jerryok826/rover-monitor/images/jpl_rover_1.jpeg

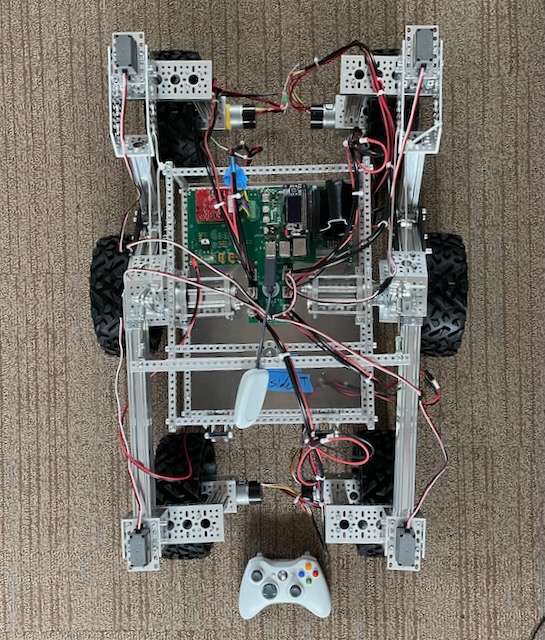
images/jpl_rover_1.jpeg
