jerryok826/rover-monitor/images/oled_board_back.jpeg

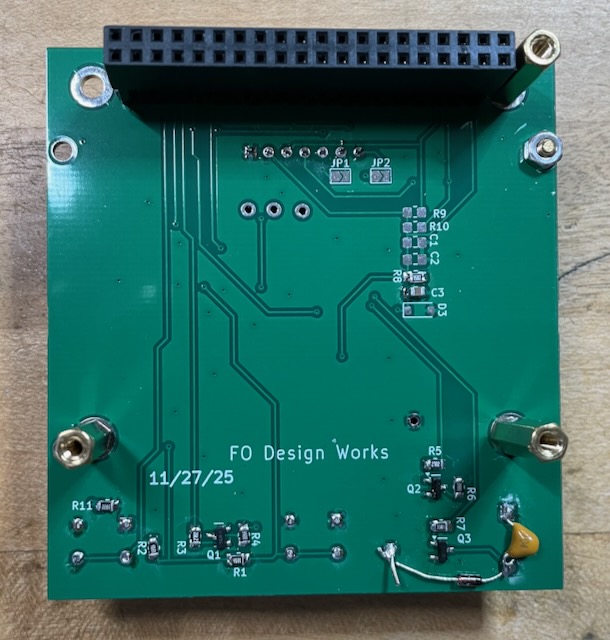
images/oled_board_back.jpeg
