jerryok826/rover-monitor/images/oled_hostname.jpeg

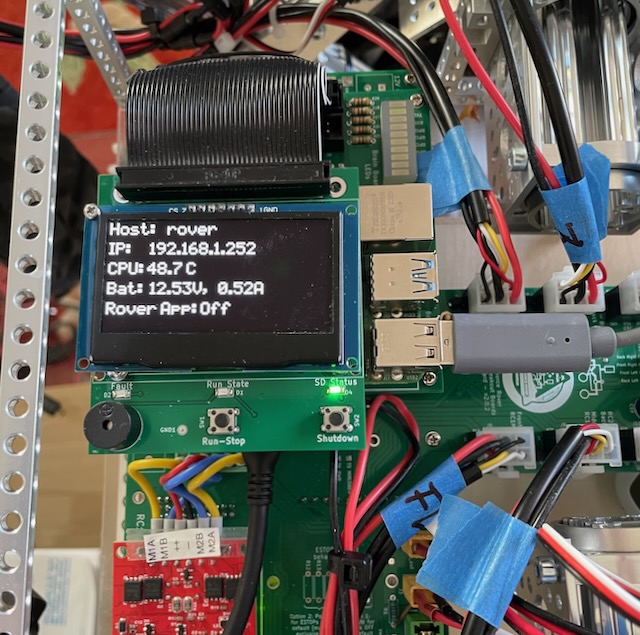
images/oled_hostname.jpeg
