jerryok826/rover-monitor/images/oled_spi.jpeg

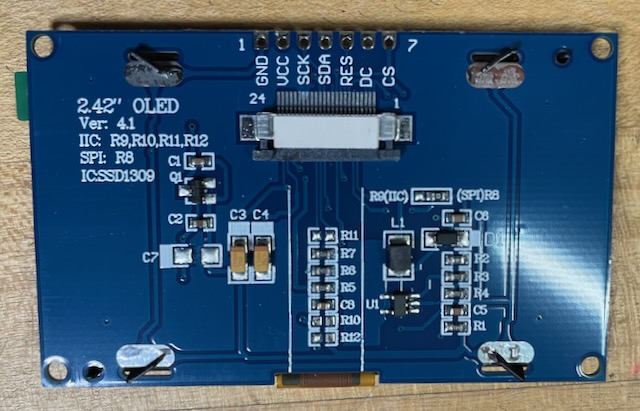
images/oled_spi.jpeg
