jerryok826/rover-monitor/images/outdoor_lawn.jpg

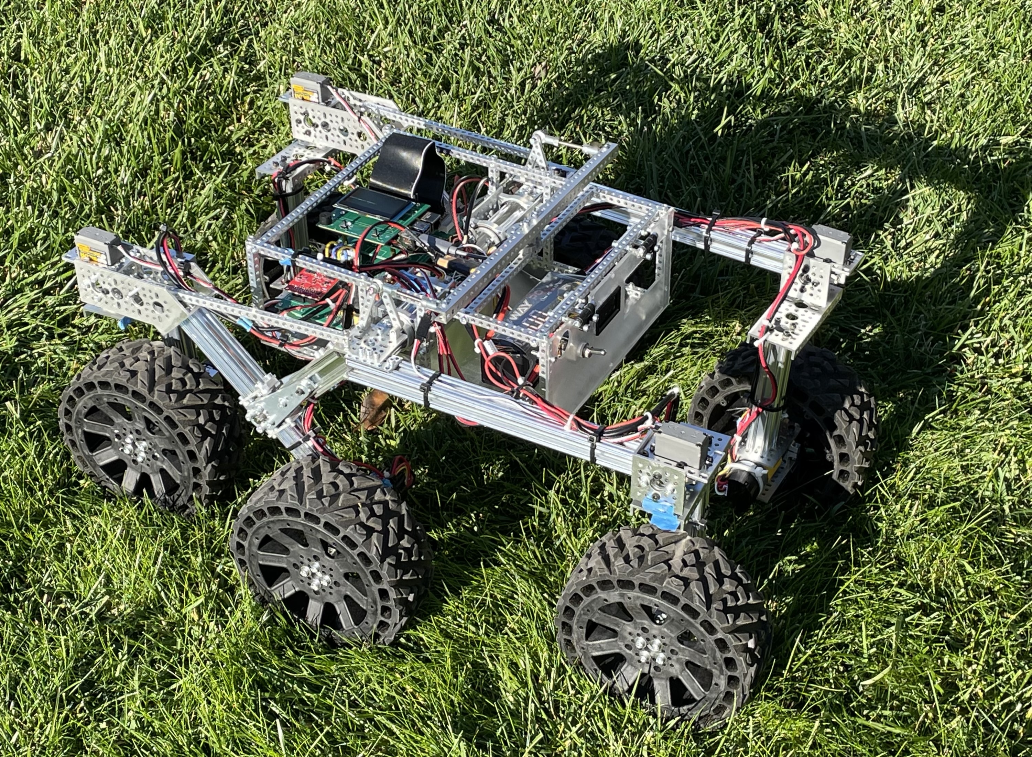
images/outdoor_lawn.jpg
