jerryok826/rover-monitor/images/prototype_2.jpeg

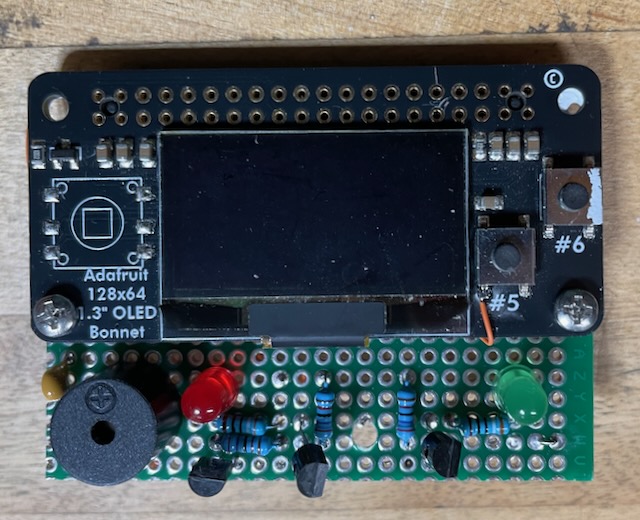
images/prototype_2.jpeg
