jerryok826/rover-monitor/images/prototype_back_2.jpeg

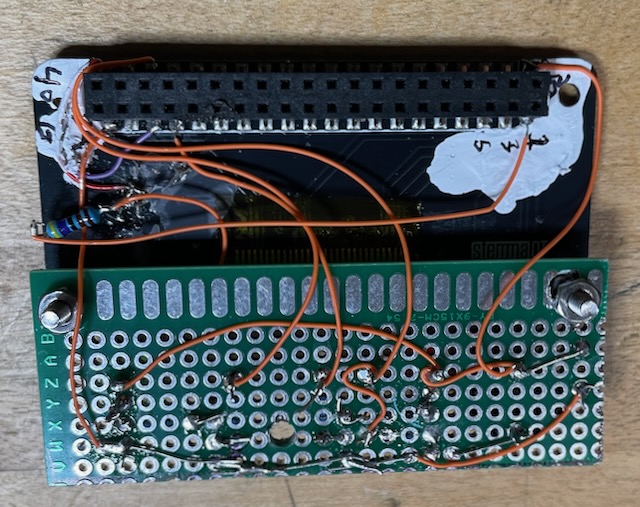
images/prototype_back_2.jpeg
