jerryok826/rover-monitor/images/rover_monitor_r2.jpg

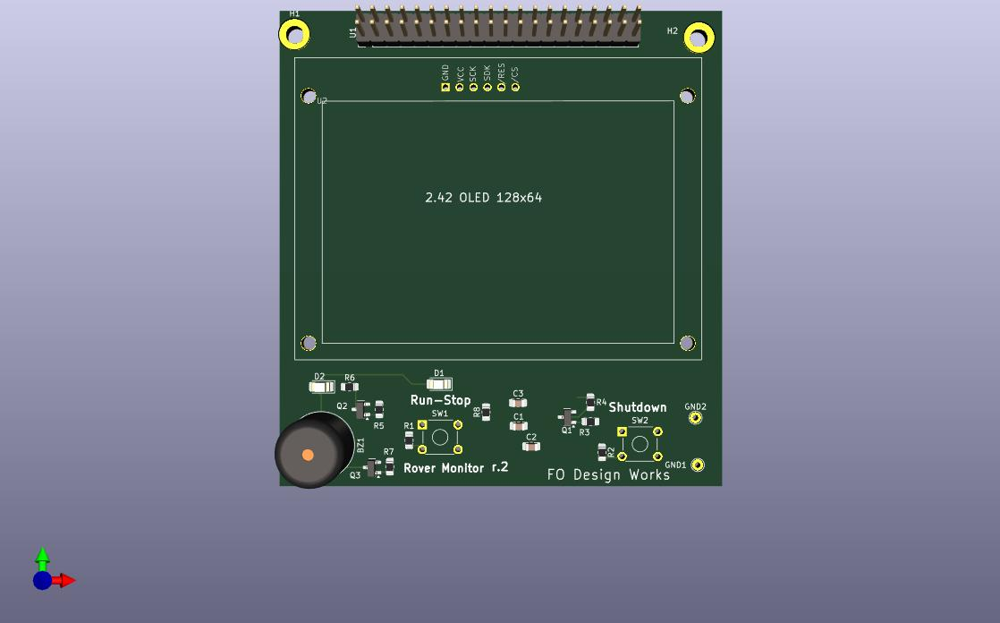
images/rover_monitor_r2.jpg
