jerryok826/rover-monitor/images/rover_monitor_r2_front.jpg

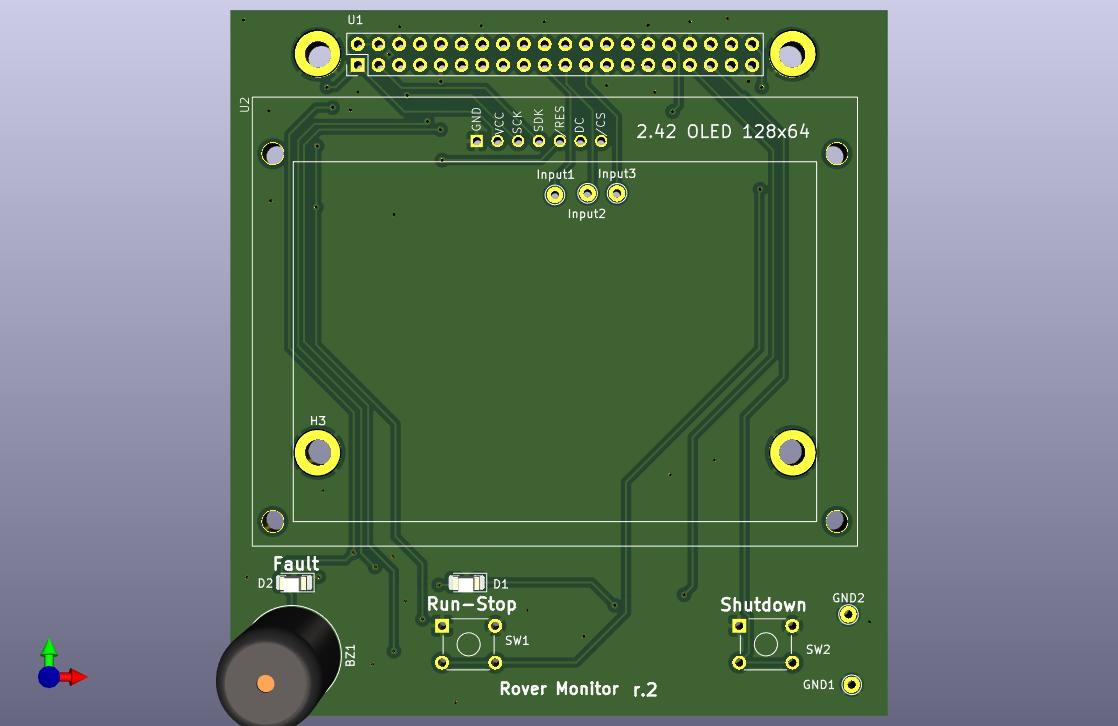
images/rover_monitor_r2_front.jpg
