jerryok826/rover-monitor/images/outside_testing_1.png

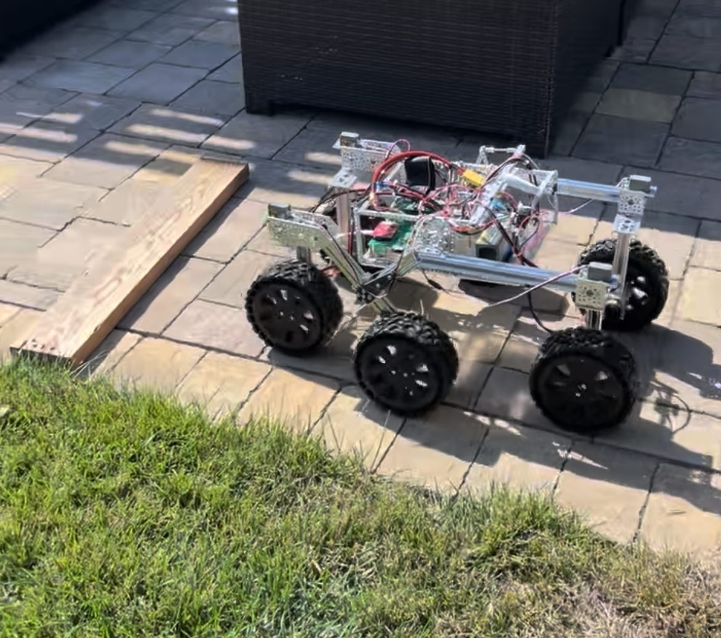
images/outside_testing_1.png
