jerryok826/rover-monitor/images/i2c_changes.jpeg

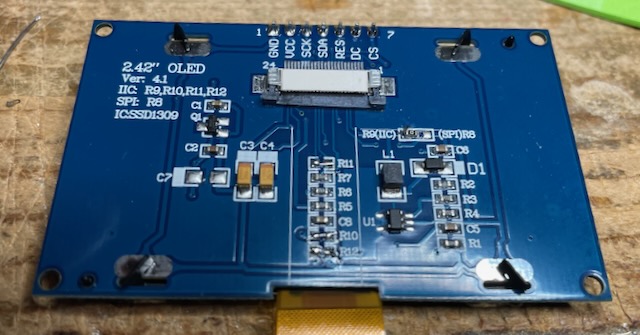
images/i2c_changes.jpeg
